crehmann/TPS42/Assets/trackpoint_back.jpg

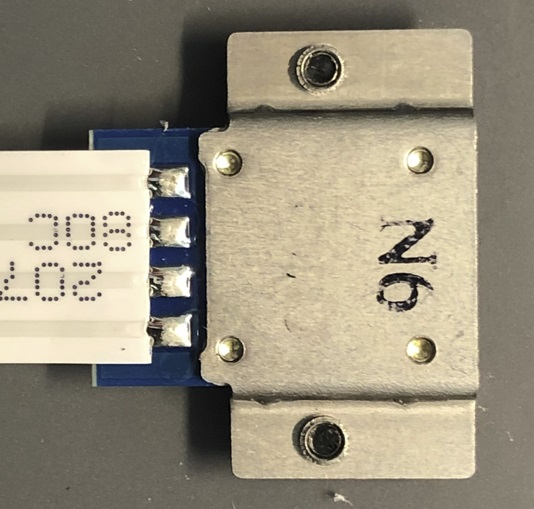
Assets/trackpoint_back.jpg
