crehmann/TPS42/Assets/trackpoint_front.jpg

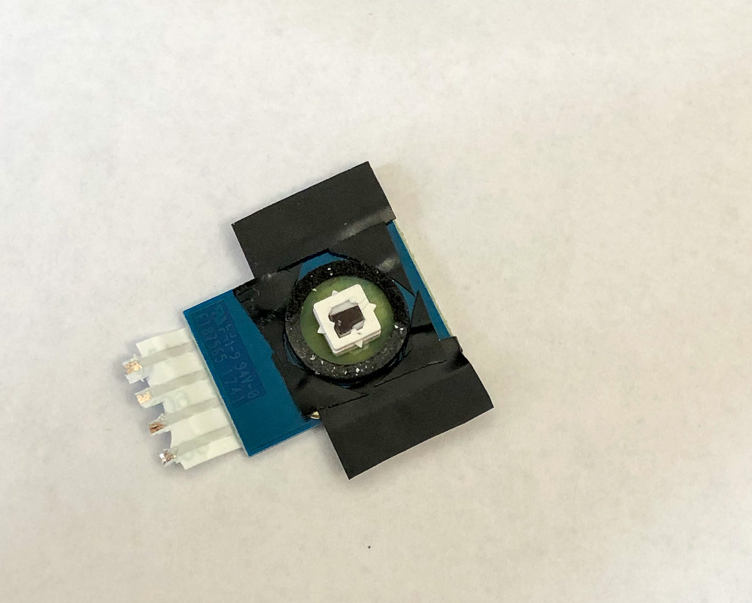
Assets/trackpoint_front.jpg
