crehmann/TPS42/Assets/trackpoint_labret.jpg

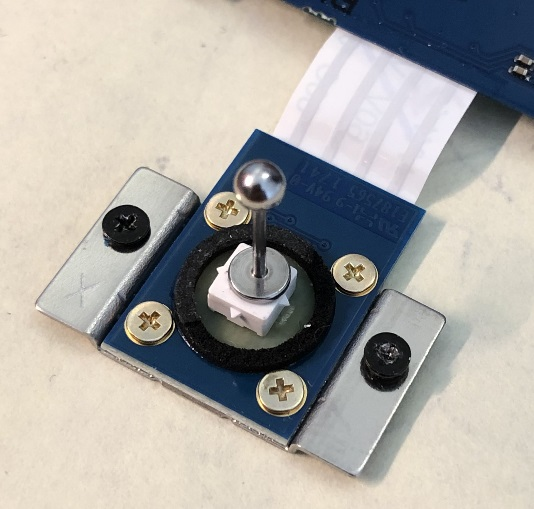
Assets/trackpoint_labret.jpg
