crehmann/TPS42/Assets/wired_case_acryic.jpg

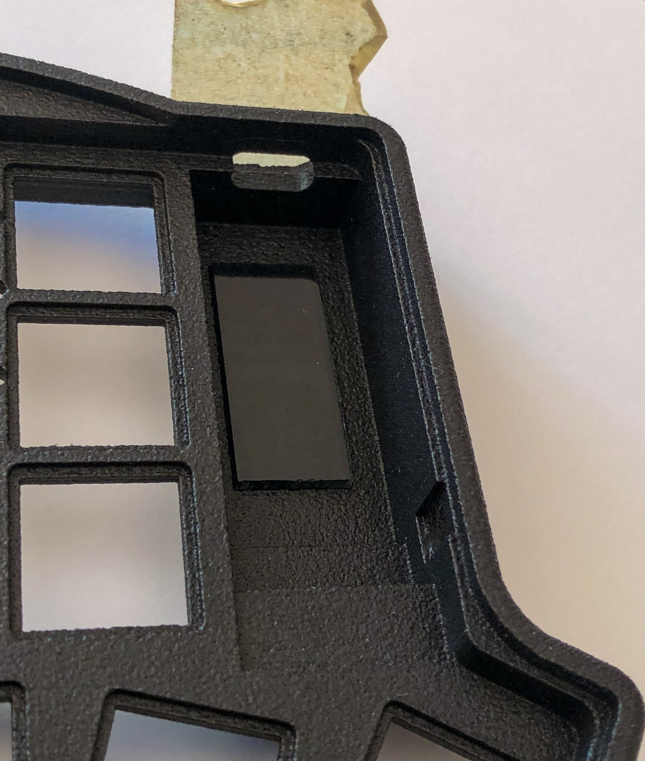
Assets/wired_case_acryic.jpg
