crehmann/TPS42/Assets/wired_case_front.jpg

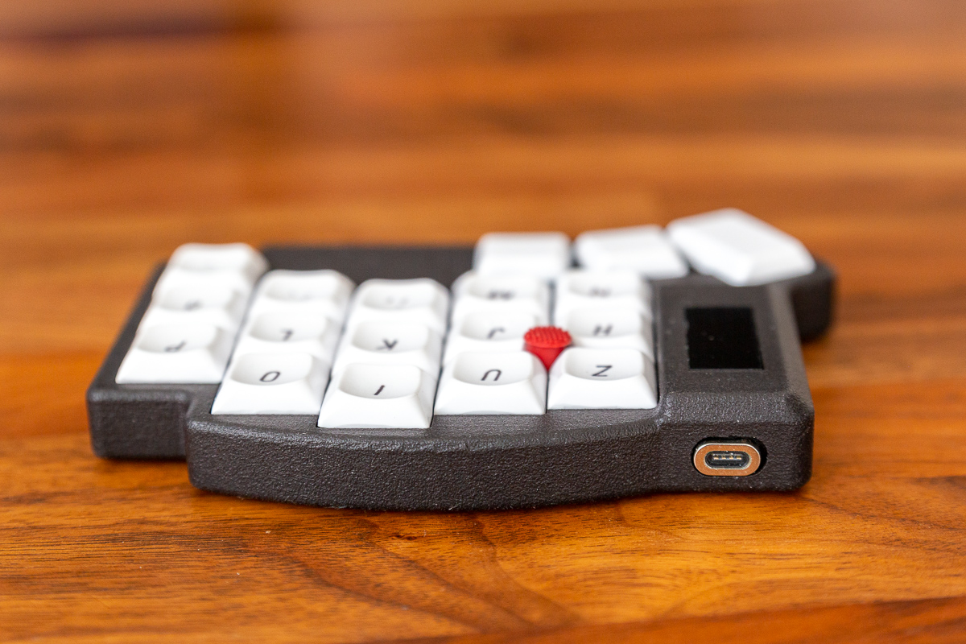
Assets/wired_case_front.jpg
