crehmann/TPS42/Assets/wired_pcb_back.jpg

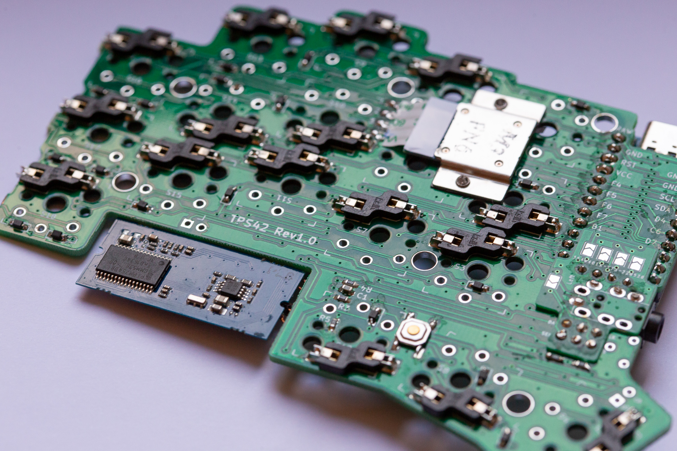
Assets/wired_pcb_back.jpg
