crehmann/TPS42/Assets/wired_pcb_shield_closeup.jpg

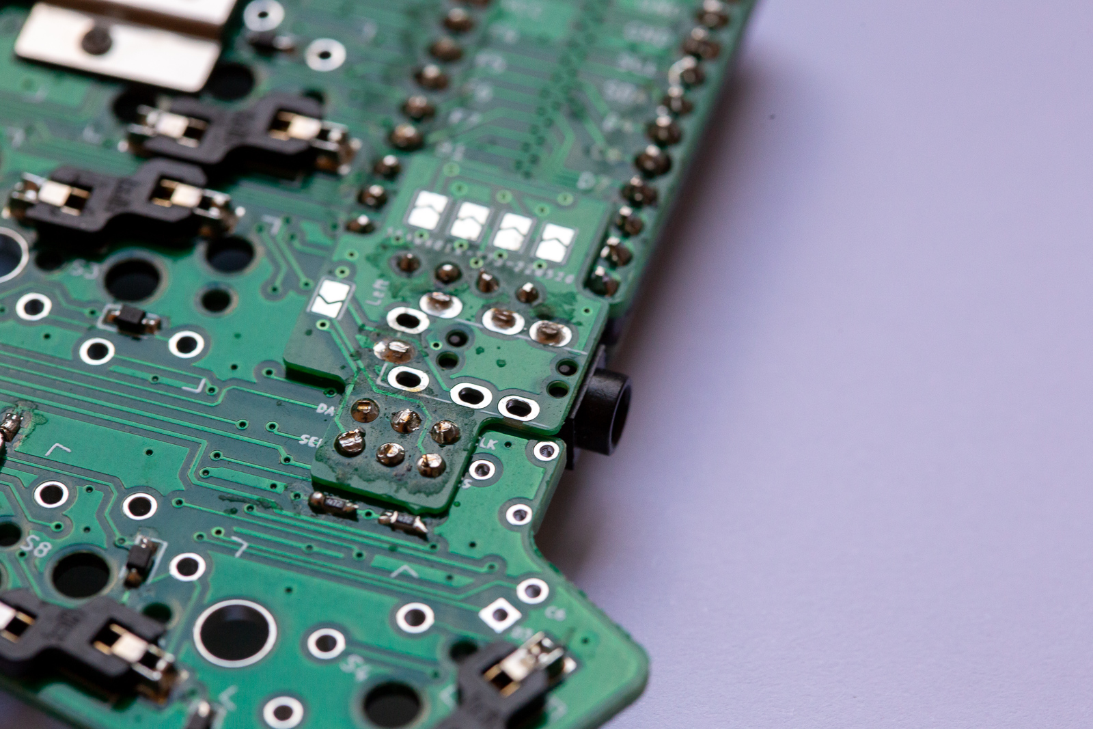
Assets/wired_pcb_shield_closeup.jpg
