crehmann/TPS42/Assets/wired_switches.jpg

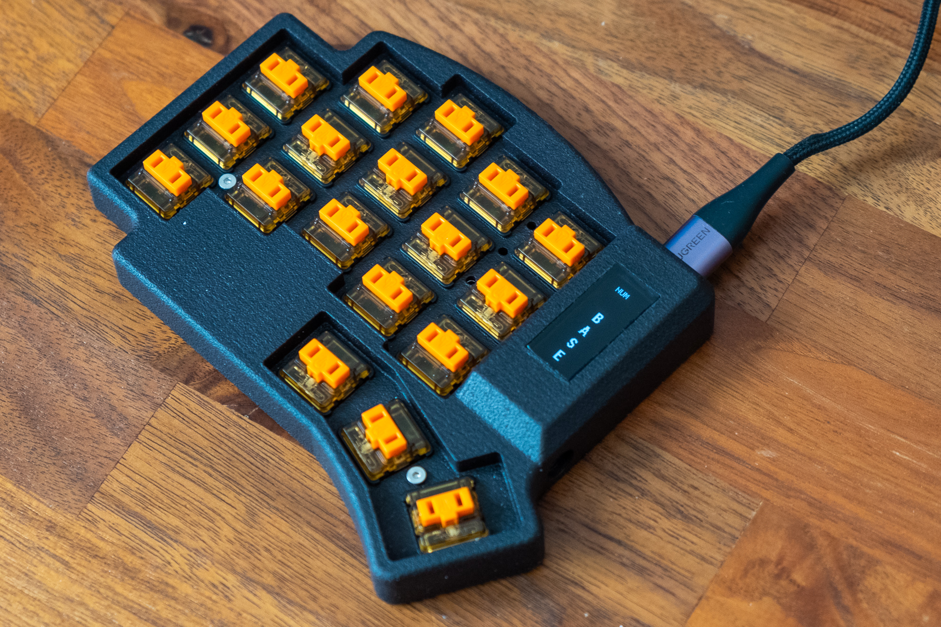
Assets/wired_switches.jpg
