crehmann/TPS42/Assets/wired_top.jpg

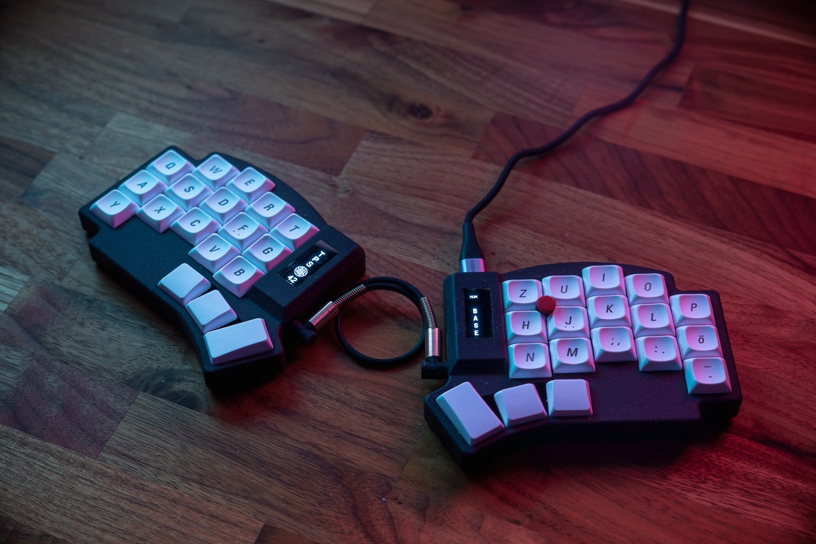
Assets/wired_top.jpg
