crehmann/TPS42/Assets/wireless_case_front.jpg

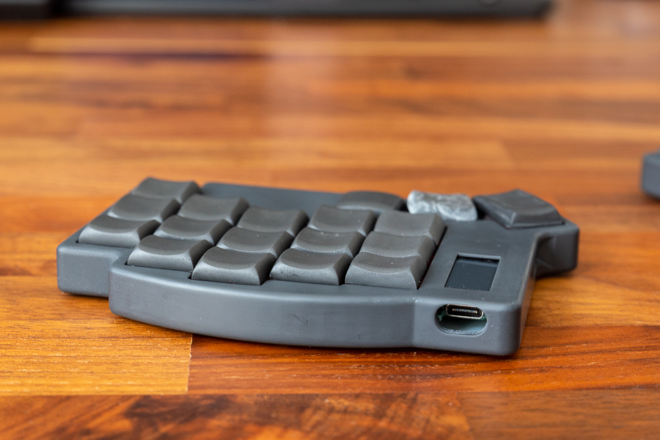
Assets/wireless_case_front.jpg
