crehmann/TPS42/Assets/wireless_case_lcd.jpg

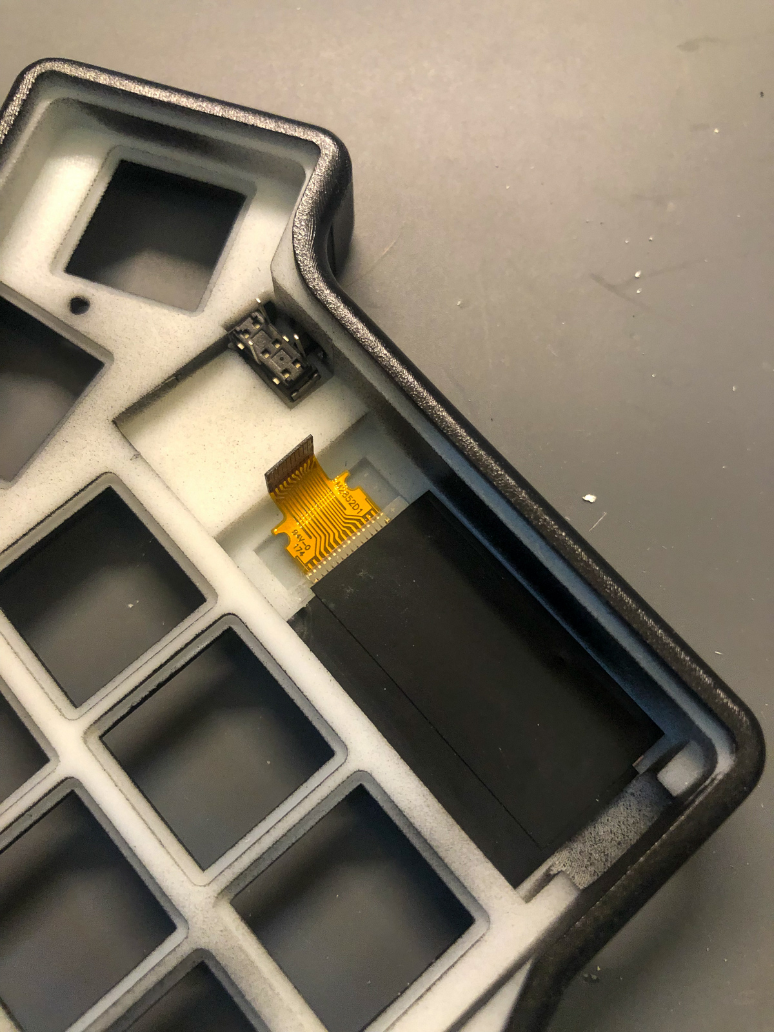
Assets/wireless_case_lcd.jpg
