crehmann/TPS42/Assets/wireless_case_pwr_switch.jpg

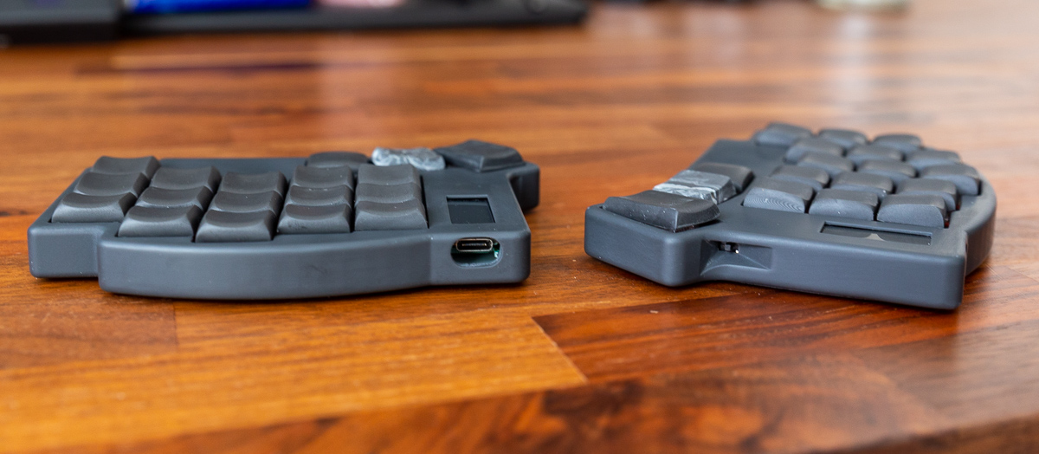
Assets/wireless_case_pwr_switch.jpg
