crehmann/TPS42/Assets/wireless_case_top.jpg

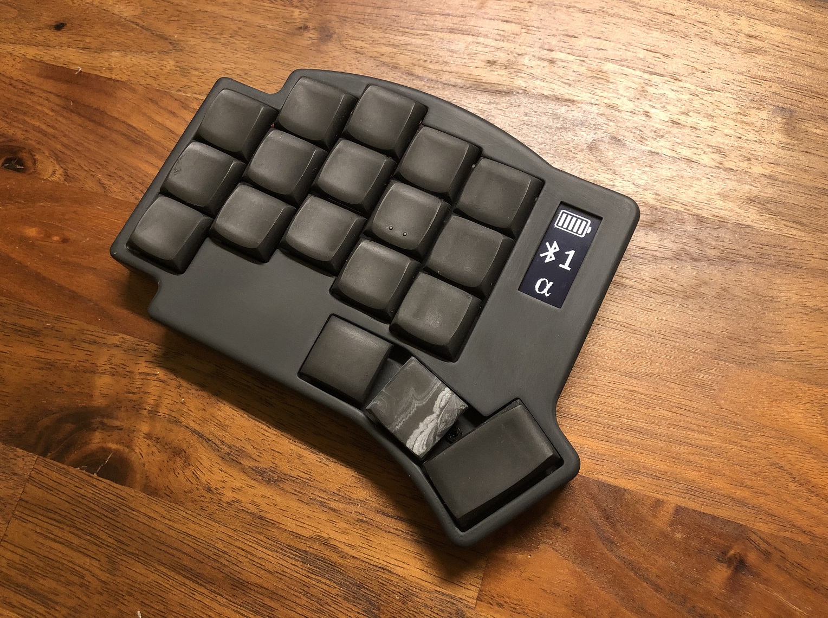
Assets/wireless_case_top.jpg
