crehmann/TPS42/Assets/wireless_pcb_side.jpg

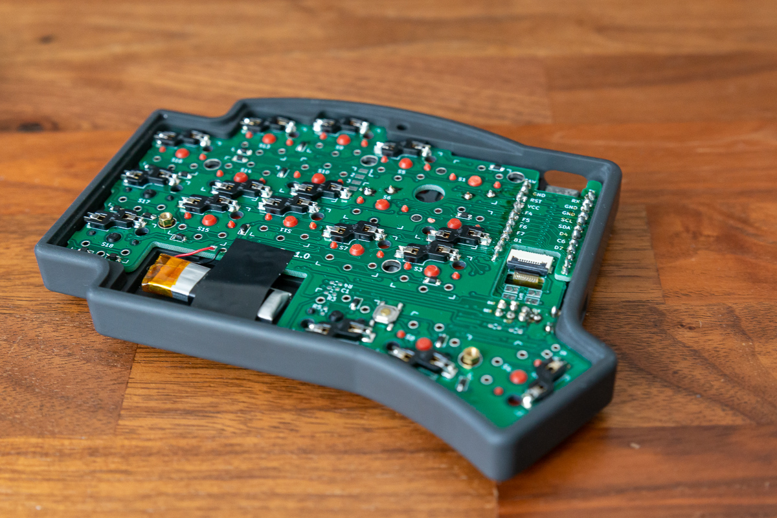
Assets/wireless_pcb_side.jpg
