crehmann/TPS42/Assets/wireless_top.jpg

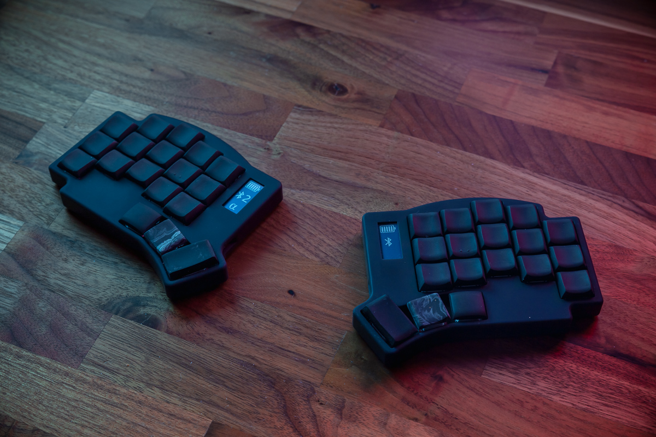
Assets/wireless_top.jpg
